little-chef/ScantronicAlarmRemoteControl/schematics/esp32-scantronic-adapter.kicad_sch

## KiCad design schematics/esp32-scantronic-adapter.kicad_sch (2024-01-31)

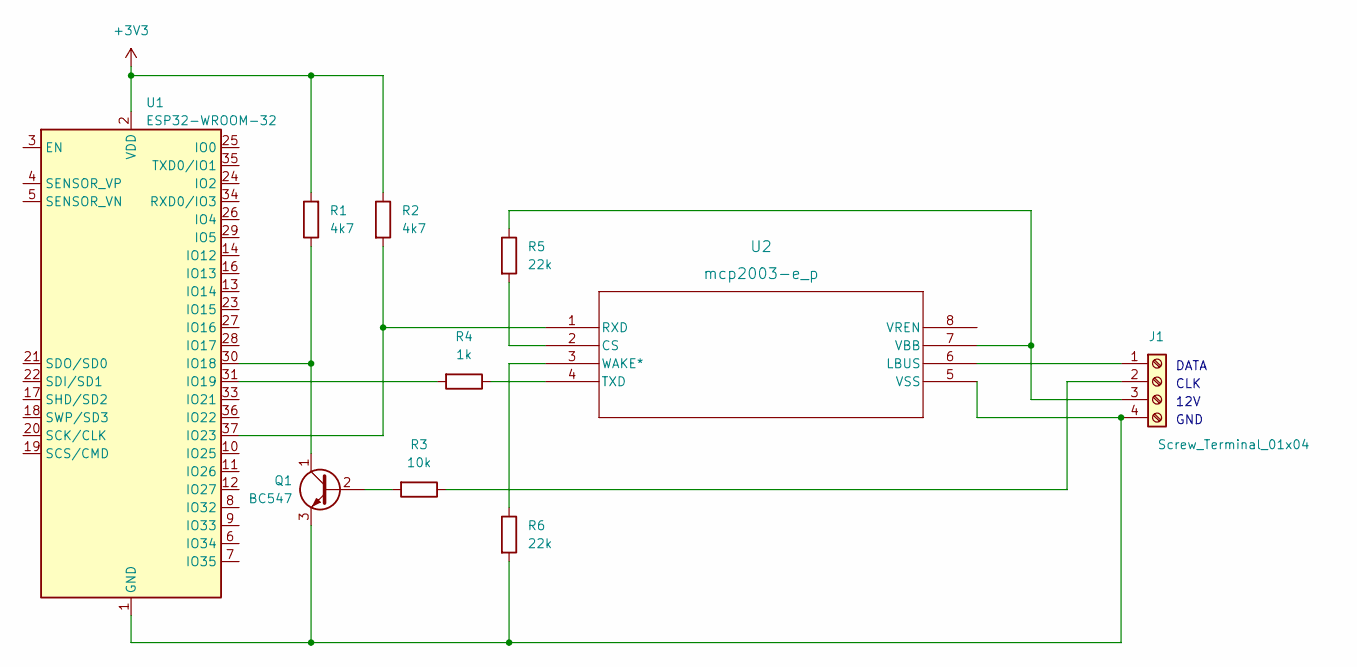
[picture p6: schematic esp32-scantronic-adapter.kicad_sch]

Parts:
J1: Screw_Terminal_01x04
Q1: BC547; TO-92_Inline
R1, R2: 4k7
R3: 10k
R4: 1k
R5, R6: 22k
U1: ESP32-WROOM-32
U2: mcp2003-e_p; PDIP8_300MC_MCH

Connections:
+3V3: R1.2, R2.1, U1.2 (VDD)
unnamed: J1.1, U2.6 (LBUS)
unnamed: J1.2, R3.1
unnamed: J1.3, R5.1, U2.7 (VBB)
unnamed: J1.4, Q1.3 (E), R6.2, U1.1 (GND), U1.15 (GND), U1.38 (GND), U1.39 (GND), U2.5 (VSS)
unnamed: Q1.1 (C), R1.1, U1.30 (IO18)
unnamed: Q1.2 (B), R3.2
unnamed: R2.2, U1.37 (IO23), U2.1 (RXD)
unnamed: R4.1, U2.4 (TXD)
unnamed: R4.2, U1.31 (IO19)
unnamed: R5.2, U2.2 (CS)
unnamed: R6.1, U2.3 (WAKE*)

Notes on the sheet:
DATA
CLK
12V
GND
